Nandish-KK/Precision_Reference/Photos/ScreenImg_FB_Filter.png

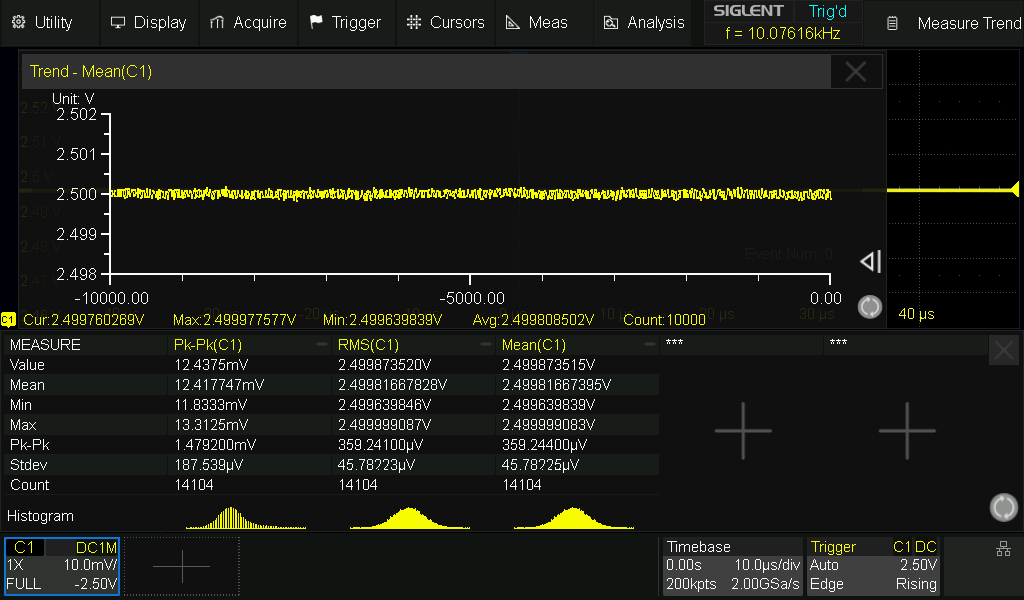
Photos/ScreenImg_FB_Filter.png
