Nandish-KK/Precision_Reference/Photos/ScreenImg_output_ring.png

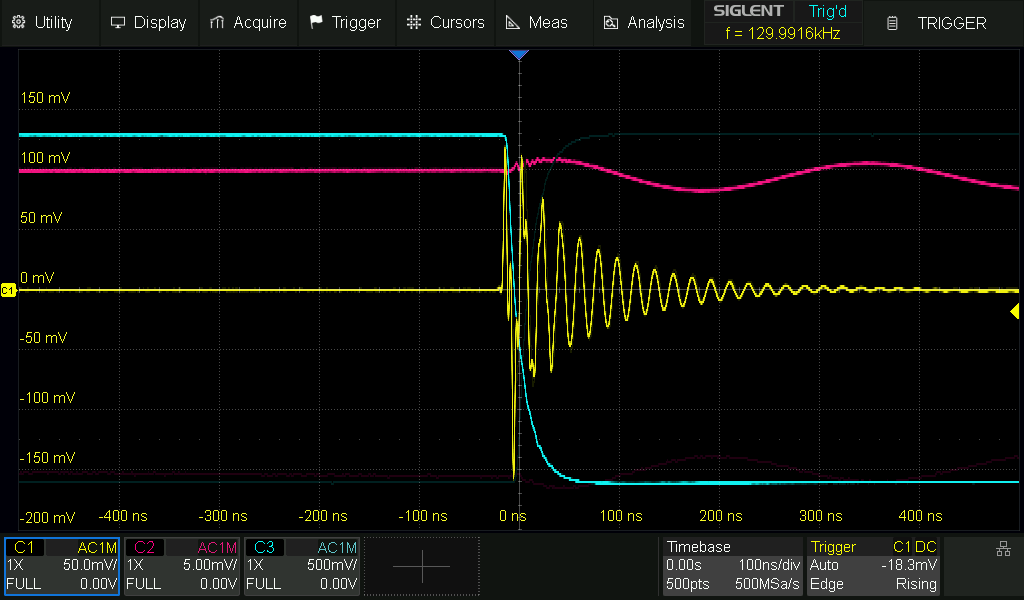
Photos/ScreenImg_output_ring.png
