Nandish-KK/Precision_Reference/Photos/ScreenImg_Quiescent.png

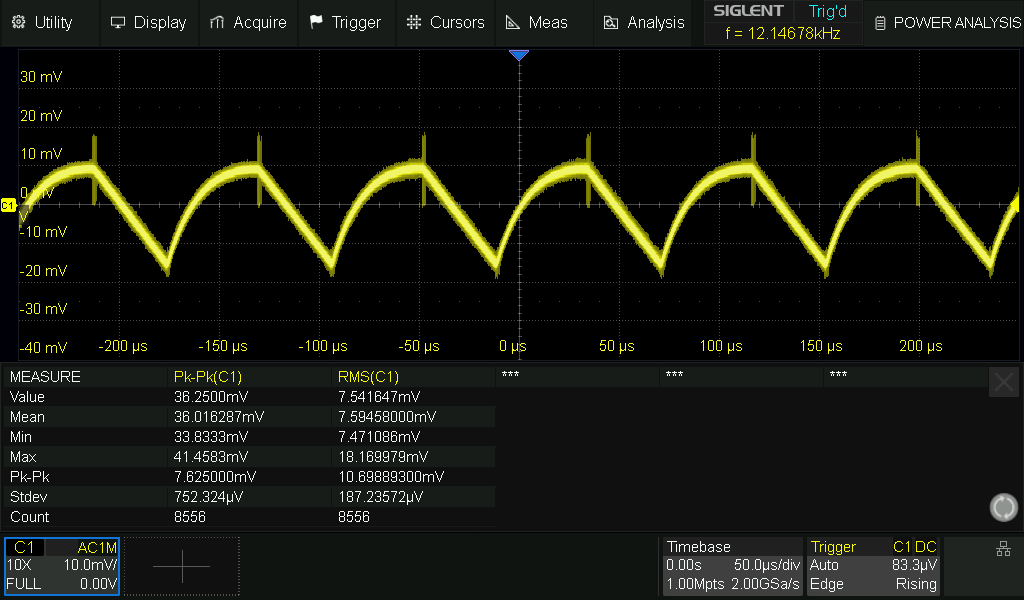
Photos/ScreenImg_Quiescent.png
