Nandish-KK/Precision_Reference/Photos/ScreenImg_RC_Filter.png

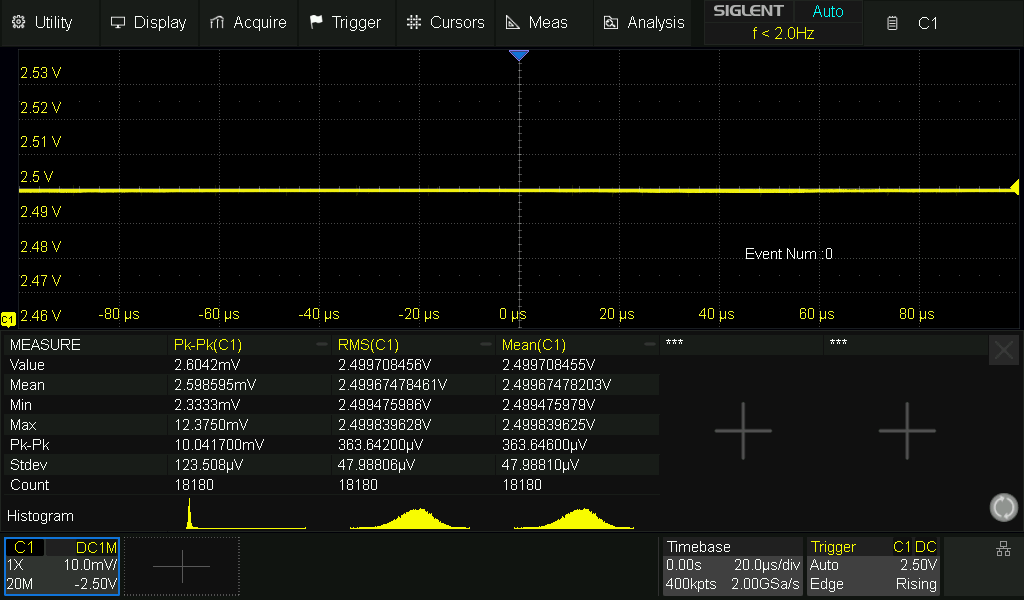
Photos/ScreenImg_RC_Filter.png
